dawsonjon/OpenXcvr/images/analyser.png

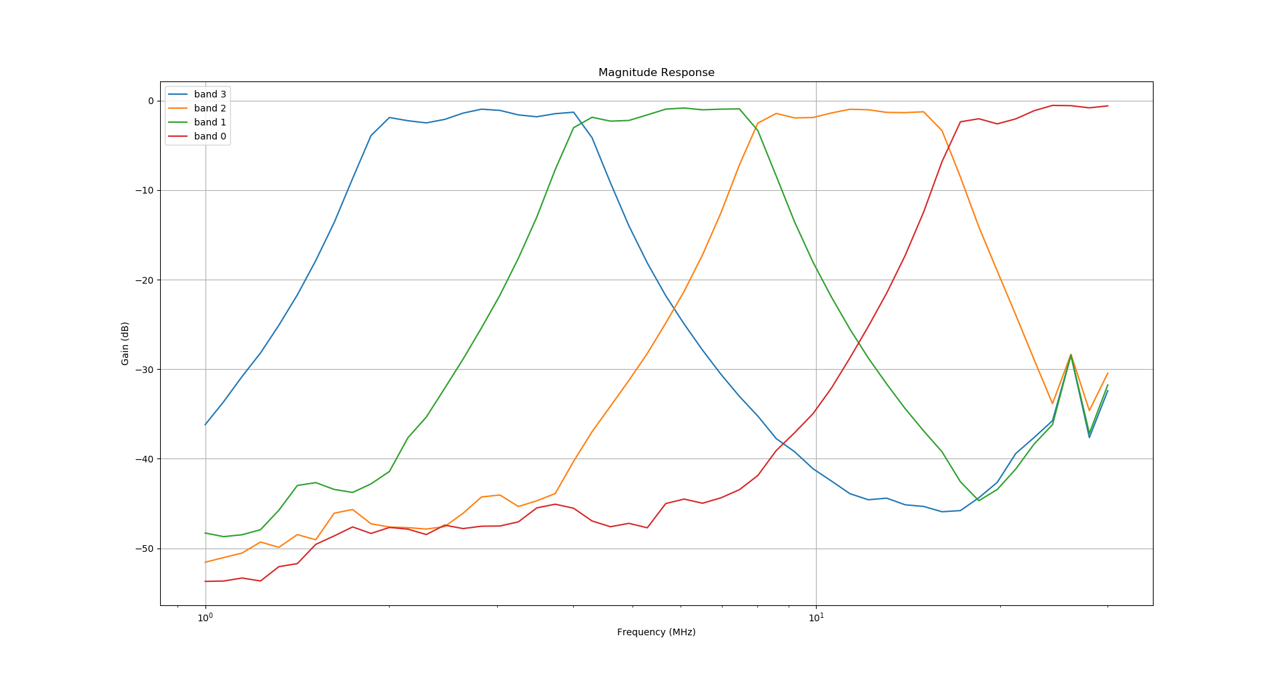
images/analyser.png
