dawsonjon/OpenXcvr/images/magnitude_estimation.png

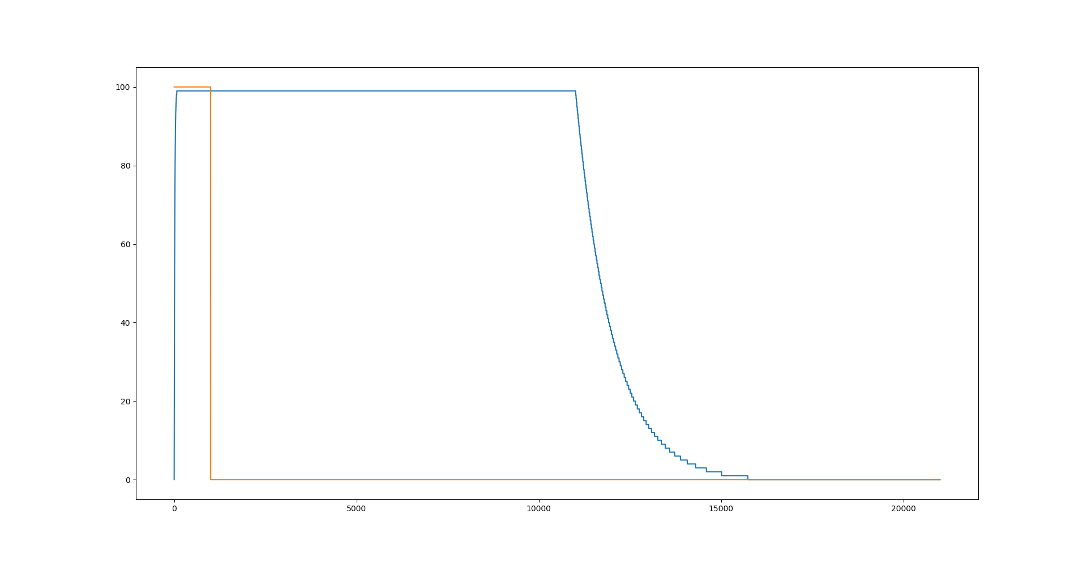
images/magnitude_estimation.png
